cytan299/Ultrasonic_Screwdriver/STL/sonic_case/push_button.stl

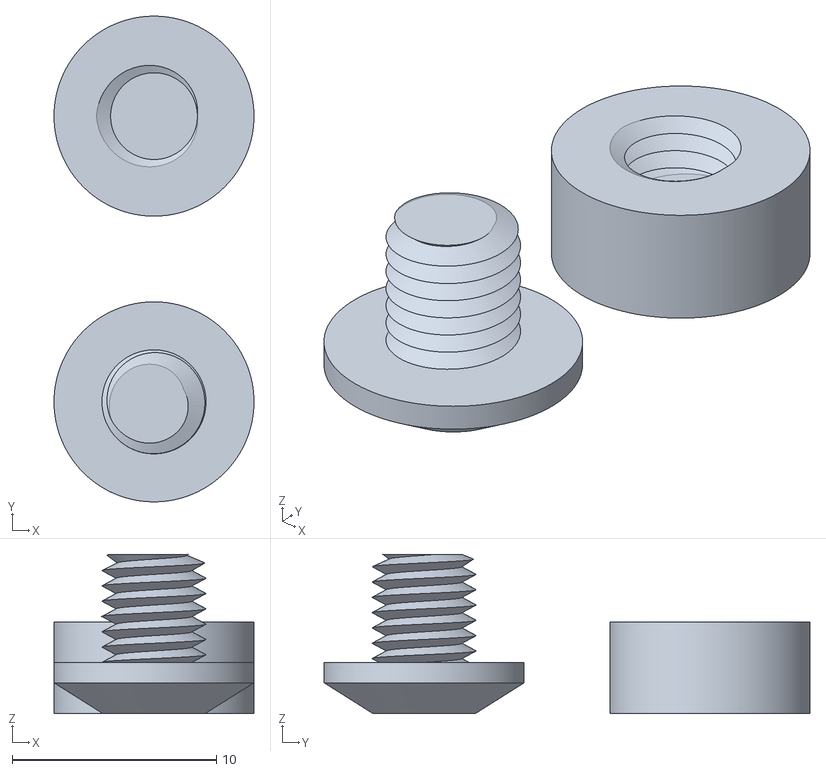
[picture p17: CAD file, 2023-10-07]
STL/sonic_case/push_button.stl
9.80 x 23.8 x 7.81
