cytan299/Ultrasonic_Screwdriver/STL/sonic_case/slipcap.stl

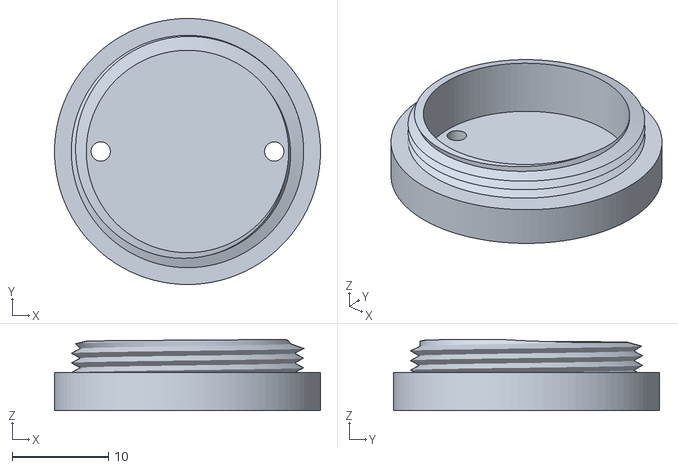
[picture p18: CAD file, 2023-10-07]
STL/sonic_case/slipcap.stl
27.6 x 27.6 x 7.41
