cytan299/Ultrasonic_Screwdriver/STL/sonic_case/outer_upper_case.stl

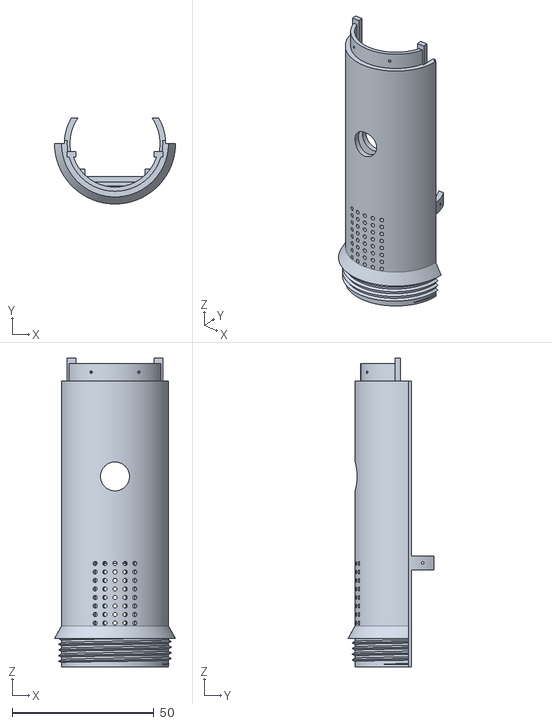
[picture p19: CAD file, 2023-10-07]
STL/sonic_case/outer_upper_case.stl
42.7 x 30.3 x 108.9
