cytan299/Ultrasonic_Screwdriver/STL/sonic_case/outer_lower_case.stl

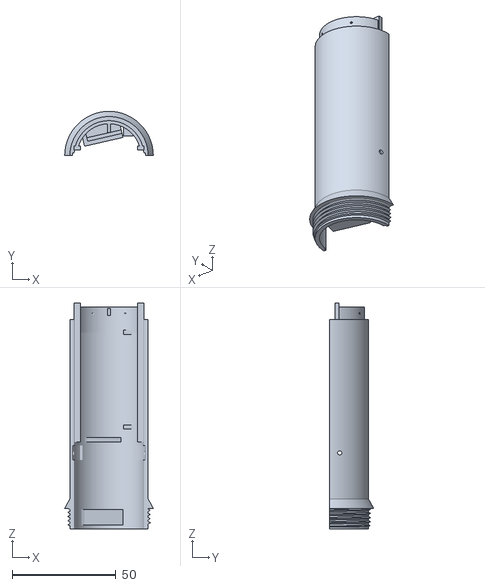
[picture p20: CAD file, 2023-10-07]
STL/sonic_case/outer_lower_case.stl
42.7 x 21.3 x 108.9
