cytan299/Ultrasonic_Screwdriver/STL/sonic_case/inner_lower_case.stl

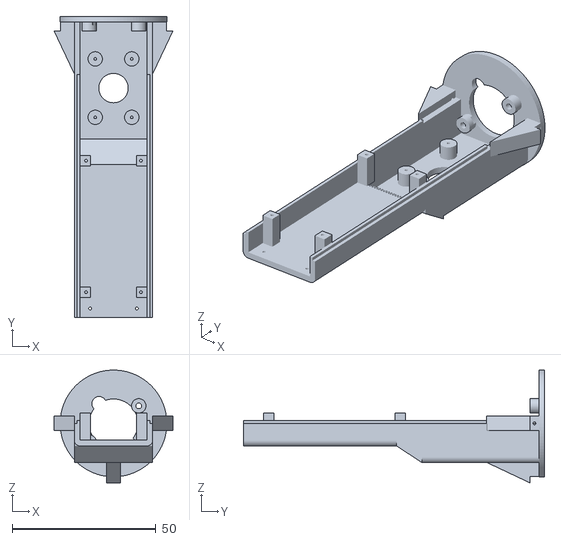
[picture p21: CAD file, 2023-10-07]
STL/sonic_case/inner_lower_case.stl
41.4 x 104.7 x 39.2
