cytan299/Ultrasonic_Screwdriver/STL/sonic_case/spring_crossbar.stl

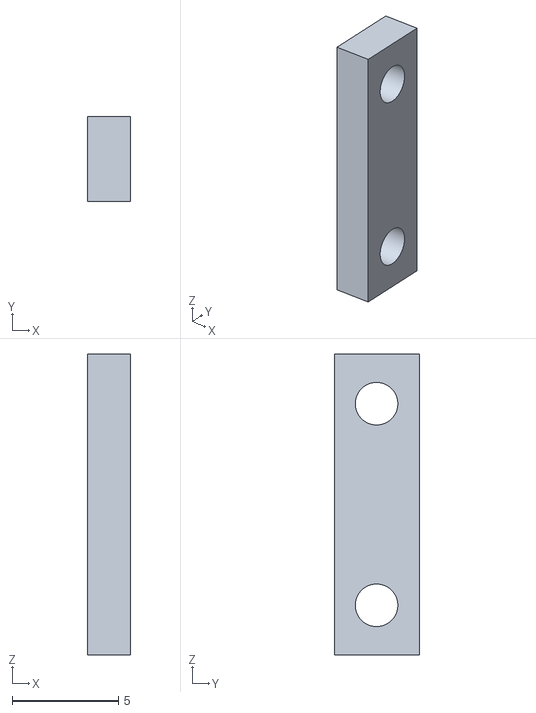
[picture p22: CAD file, 2023-10-07]
STL/sonic_case/spring_crossbar.stl
2.00 x 4.00 x 14.1
