cytan299/Ultrasonic_Screwdriver/ultrasonic_screwdriver/audio.ino

/*$Id$*/
/*
    audio part of the controller code for the Adafruit ESP32-S3
    reverse TFT Feather
    Copyright (C) 2023 C.Y. Tan
    Contact: cytan299@yahoo.com

    This file is part of ultrasonic_screwdriver

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
    You should have received a copy of the GNU General Public License
    along with audio.  If not, see
    <http://www.gnu.org/licenses/>.

*/

/* operating system header files (use <> for make depend) */

/* general system header files (use "" for make depend) */

#include "AudioTools.h"

/* local include files (use "") */

/*
	Ultrasonic screwdriver sound created by C.Y. Tan
 */

int16_t sonicdriver_array[]={-12088, 9278, 841, -2755, -658, -4653, 16768, -15471, -7483, 29937, -24067, -6363, 
27680, -16781, -11496, 23758, -7620, -16771, 22625, -5680, -14798, 18851, -5277, -10297, 
13098, -3489, -5664, 4429, 3377, -6004, -1344, 10899, -12156, 3878, 6021, -10076, 
7468, -2062, -1773, 1424, 2021, -3253, -1947, 9251, -8210, -3934, 14671, -9118, 
-10051, 22672, -14045, -7435, 20410, -15110, 1837, 4541, -2099, 377, -4961, 9375, 
-4429, -7341, 11702, -19, -16567, 17069, 3129, -22801, 18895, 3564, -16178, 3635, 
15606, -13355, -10835, 28710, -19261, -6400, 21157, -14255, -689, 6025, 430, -7149, 
4303, 5637, -11171, 4823, 6957, -9436, -2388, 14979, -11521, -5645, 16448, -9169, 
-4073, 5067, 4317, -5688, -7158, 16647, -5652, -15864, 20781, -294, -22411, 19938, 
5101, -23293, 14827, 7374, -16193, 4859, 7500, -4219, -6922, 7436, 4041, -10424, 
2365, 7328, -2535, -11707, 14935, 724, -19311, 20917, -5092, -12088, 9278, 841, 
-2755, -658, -4653, 16768, -15471, -7483, 29937, -24067, -6363, 27680, -16781, -11496, 
23758, -7620, -16771, 22625, -5680, -14798, 18851, -5277, -10297, 13098, -3489, -5664, 
4429, 3377, -6004, -1344, 10899, -12156, 3878, 6021, -10076, 7468, -2062, -1773, 
1424, 2021, -3253, -1947, 9251, -8210, -3934, 14671, -9118, -10051, 22672, -14045, 
-7435, 20410, -15110, 1837, 4541, -2099, 377, -4961, 9375, -4429, -7341, 11702, 
-19, -16567, 17069, 3129, -22801, 18895, 3564, -16178, 3635, 15606, -13355, -10835, 
28710, -19261, -6400, 21157, -14255, -689, 6025, 430, -7149, 4303, 5637, -11171, 
4823, 6957, -9436, -2388, 14979, -11521, -5645, 16448, -9169, -4073, 5067, 4317, 
-5688, -7158, 16647, -5652, -15864, 20781, -294, -22411, 19938, 5101, -23293, 14827, 
7374, -16193, 4859, 7500, -4219, -6922, 7436, 4041, -10424, 2365, 7328, -2535, 
-11707, 14935, 724, -19311, 20917, -5092, -12088, 9278, 841, -2755, -658, -4653, 
16768, -15471, -7483, 29937, -24067, -6363, 27680, -16781, -11496, 23758, -7620, -16771, 
22625, -5680, -14798, 18851, -5277, -10297, 13098, -3489, -5664, 4429, 3377, -6004, 
-1344, 10899, -12156, 3878, 6021, -10076, 7468, -2062, -1773, 1424, 2021, -3253, 
-1947, 9251, -8210, -3934, 14671, -9118, -10051, 22672, -14045, -7435, 20410, -15110, 
1837, 4541, -2099, 377, -4961, 9375, -4429, -7341, 11702, -19, -16567, 17069, 
3129, -22801, 18895, 3564, -16178, 3635, 15606, -13355, -10835, 28710, -19261, -6400, 
21157, -14255, -689, 6025, 430, -7149, 4303, 5637, -11171, 4823, 6957, -9436, 
-2388, 14979, -11521, -5645, 16448, -9169, -4073, 5067, 4317, -5688, -7158, 16647, 
-5652, -15864, 20781, -294, -22411, 19938, 5101, -23293, 14827, 7374, -16193, 4859, 
7500, -4219, -6922, 7436, 4041, -10424, 2365, 7328, -2535, -11707, 14935, 724, 
-19311, 20917, -5092, -12088, 9278, 841, -2755, -658, -4653, 16768, -15471, -7483, 
29937, -24067, -6363, 27680, -16781, -11496, 23758, -7620, -16771, 22625, -5680, -14798, 
18851, -5277, -10297, 13098, -3489, -5664, 4429, 3377, -6004, -1344, 10899, -12156, 
3878, 6021, -10076, 7468, -2062, -1773, 1424, 2021, -3253, -1947, 9251, -8210, 
-3934, 14671, -9118, -10051, 22672, -14045, -7435, 20410, -15110, 1837, 4541, -2099, 
377, -4961, 9375, -4429, -7341, 11702, -19, -16567, 17069, 3129, -22801, 18895, 
3564, -16178, 3635, 15606, -13355, -10835, 28710, -19261, -6400, 21157, -14255, -689, 
6025, 430, -7149, 4303, 5637, -11171, 4823, 6957, -9436, -2388, 14979, -11521, 
-5645, 16448, -9169, -4073, 5067, 4317, -5688, -7158, 16647, -5652, -15864, 20781, 
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


/**********************************************************************
 Set up the audio stream
 **********************************************************************/  



AudioInfo info(10000, 1, 16);

I2SStream i2sStream;
VolumeStream volume(i2sStream);

/*
    1st arg: is the sound array
    infinite loop here:
    2nd arg: repeat = 0 means infinite repeat
    3rd arg: the generator is set to inactive at the end is *false*
    

*/


GeneratorFromArray<int16_t> sonicdriver_wave(sonicdriver_array,1,true);
GeneratedSoundStream<int16_t> sonicdriver_sound(sonicdriver_wave); 


StreamCopy copier(volume, sonicdriver_sound);


// Arduino Setup
void audio_setup() {

  auto config = i2sStream.defaultConfig(TX_MODE);
  config.pin_ws = 14;	// LRC
  config.pin_bck = 15;  // BCK
  config.pin_data = 16; // DIN



  config.pin_data = 16; // DIN  
  //  config.sample_rate = 44100;
  config.sample_rate = 10000; //44100;  
  config.channels = 1;
  config.bits_per_sample = 16;
  config.i2s_format = I2S_LSB_FORMAT;
  i2sStream.begin(config);

  volume.begin(config);
  volume.setVolume(0.5);
#ifdef DEBUG
  // Setup sonic driver sound
  Serial.println("setting up sonic driver sound ...");  
  sonicdriver_wave.begin(info);
  Serial.println("started...");
#endif  
}
